ajcord/Eagle-Project/instructions/Deck/1.png

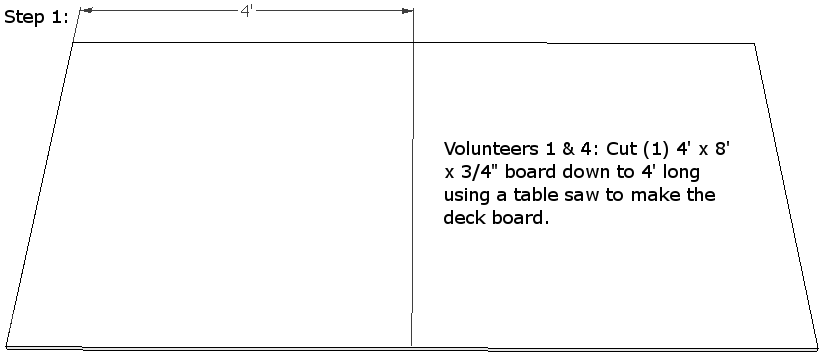
instructions/Deck/1.png
