ajcord/Eagle-Project/instructions/Deck/3.png

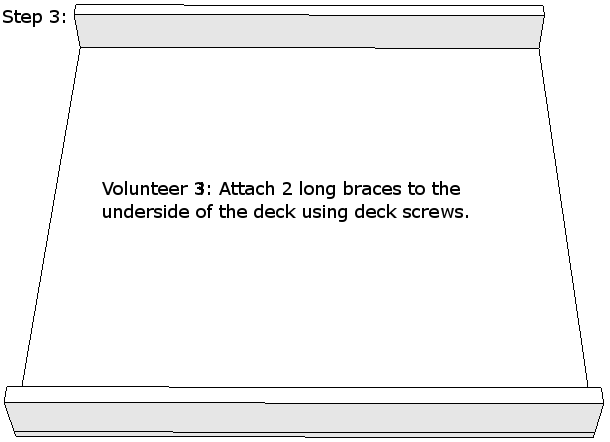
instructions/Deck/3.png
