ajcord/Eagle-Project/instructions/Deck/5.png

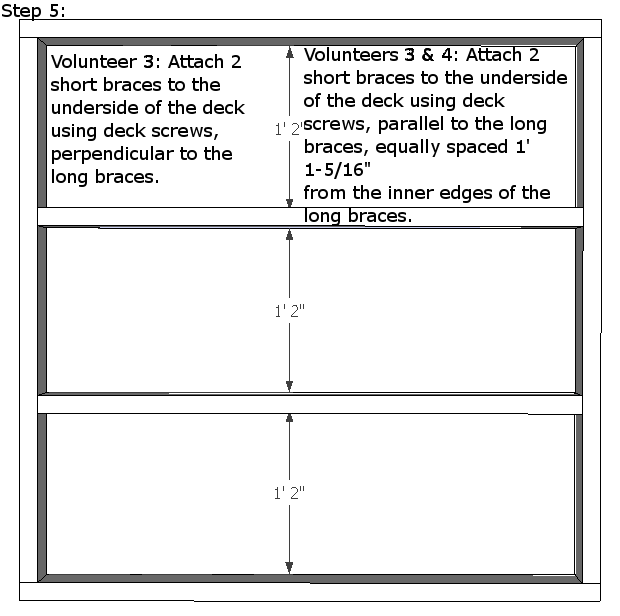
instructions/Deck/5.png
