ajcord/Eagle-Project/instructions/Deck/7.png

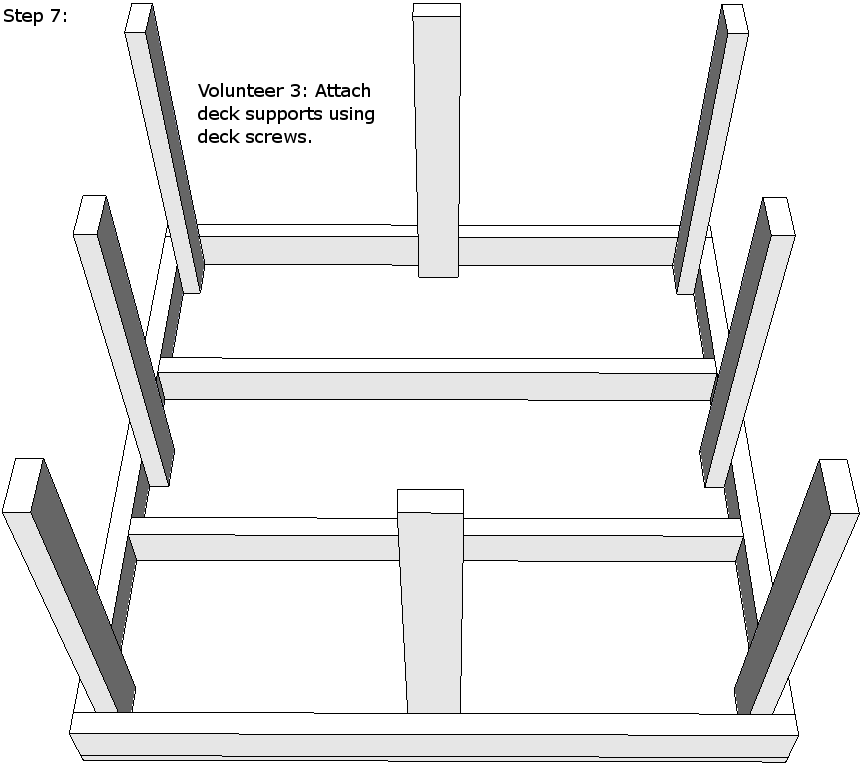
instructions/Deck/7.png
