ajcord/Eagle-Project/instructions/Denver attachment/1.png

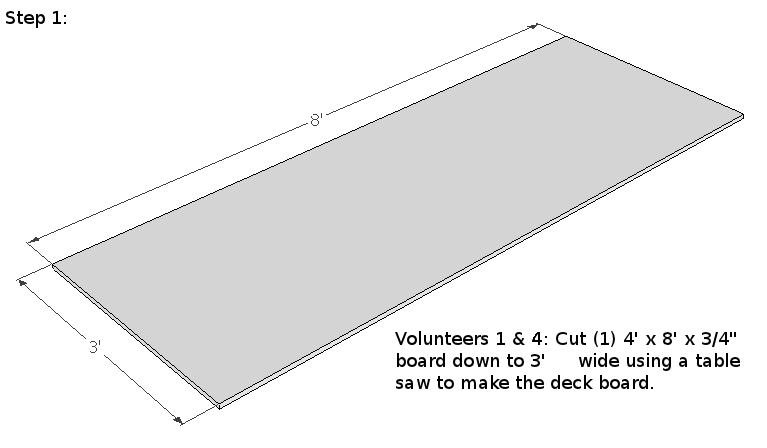
instructions/Denver attachment/1.png
