ajcord/Eagle-Project/instructions/Denver attachment/4.png

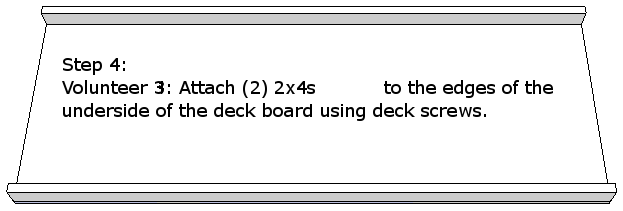
instructions/Denver attachment/4.png
