ajcord/Eagle-Project/instructions/Denver attachment/6.png

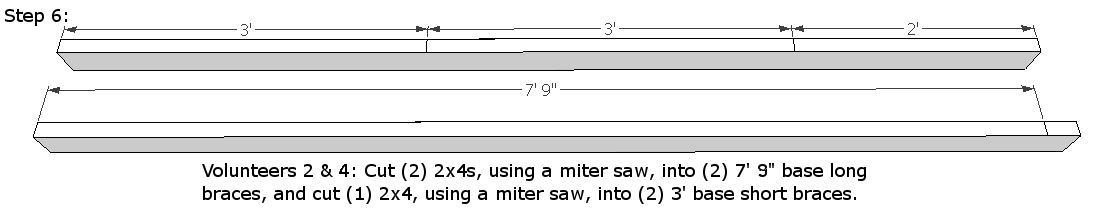
instructions/Denver attachment/6.png
