ajcord/Eagle-Project/instructions/Denver attachment/7.png

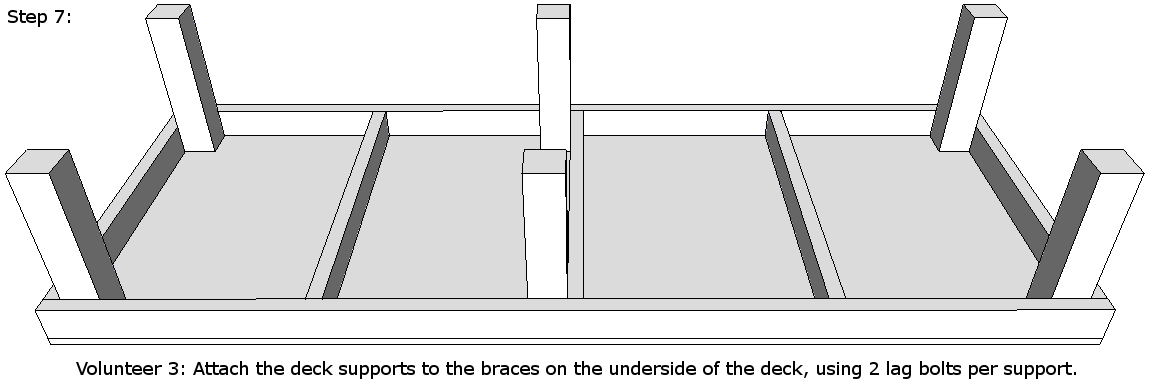
instructions/Denver attachment/7.png
