ajcord/Eagle-Project/instructions/Denver attachment/8.png

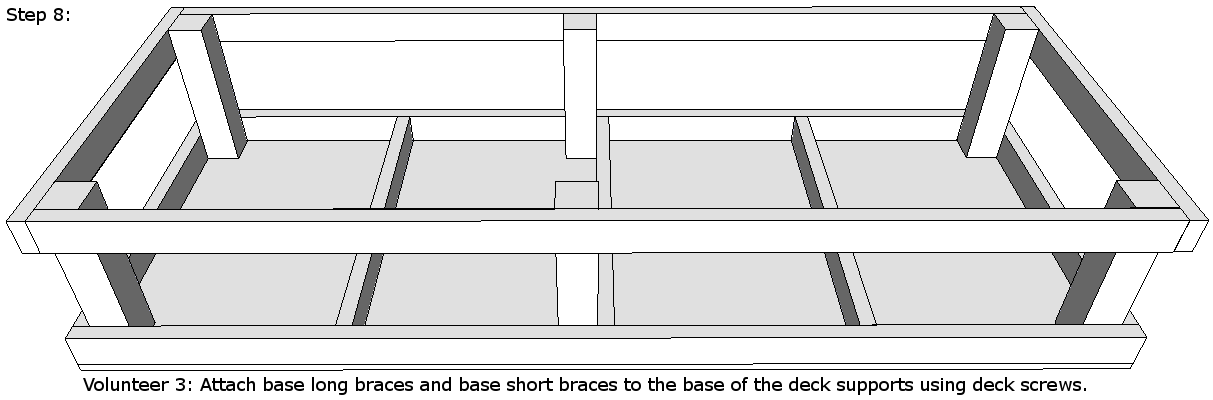
instructions/Denver attachment/8.png
