ajcord/Eagle-Project/instructions/Denver attachment/9.png

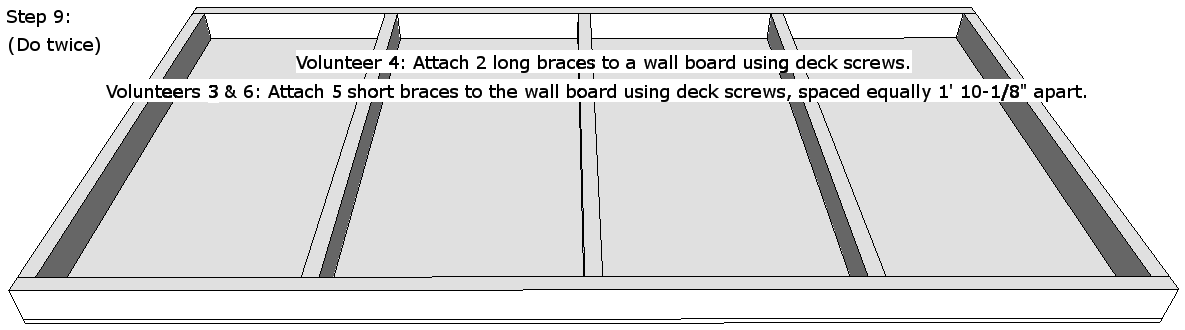
instructions/Denver attachment/9.png
