ajcord/Eagle-Project/instructions/Denver attachment/10.png

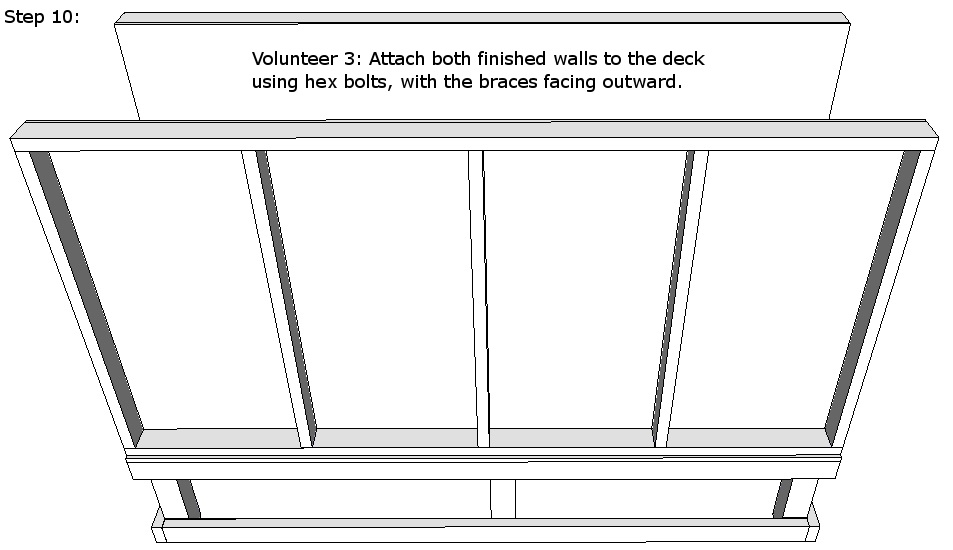
instructions/Denver attachment/10.png
