ajcord/Eagle-Project/instructions/Denver attachment/11.png

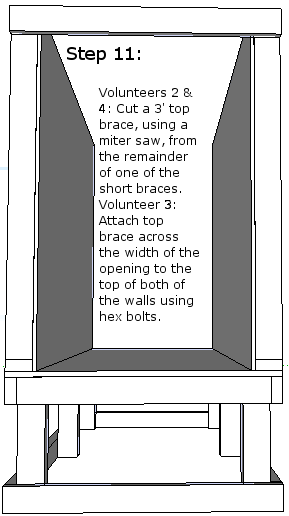
instructions/Denver attachment/11.png
