ajcord/Eagle-Project/instructions/Extras/3.png

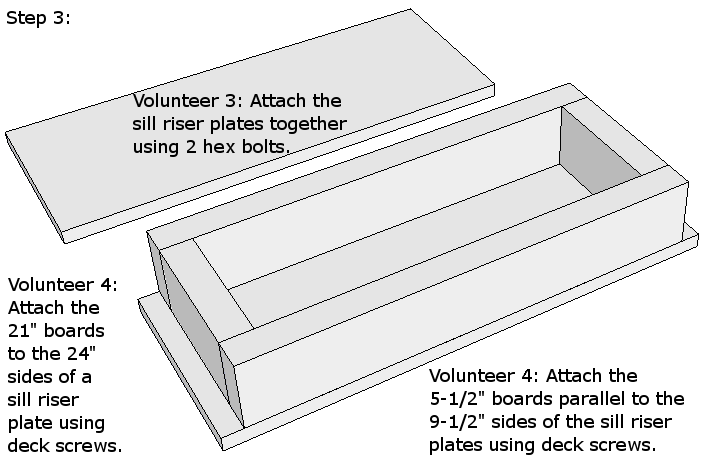
instructions/Extras/3.png
