ajcord/Eagle-Project/instructions/Main wall/1.png

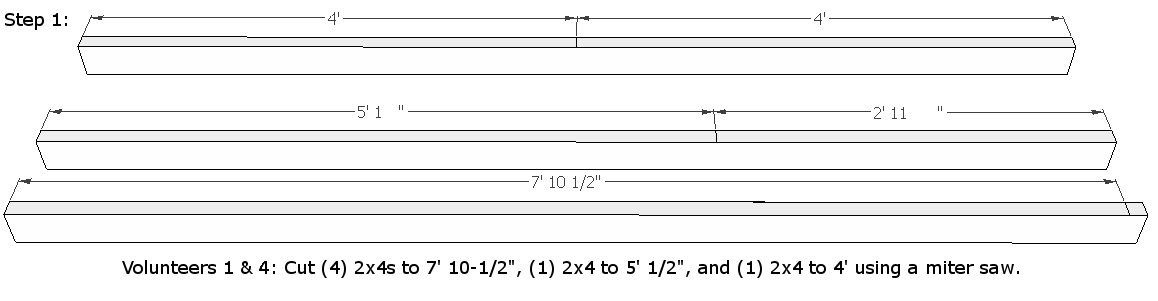
instructions/Main wall/1.png
