ajcord/Eagle-Project/instructions/Main wall/2.png

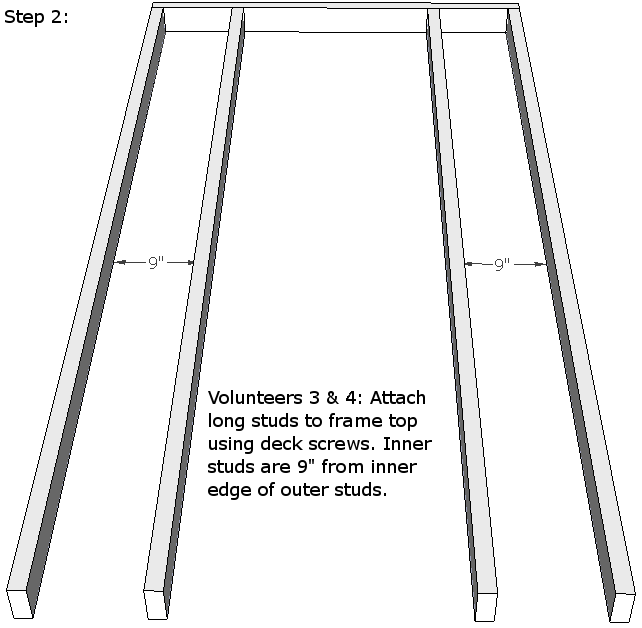
instructions/Main wall/2.png
