ajcord/Eagle-Project/instructions/Main wall/4-2.png

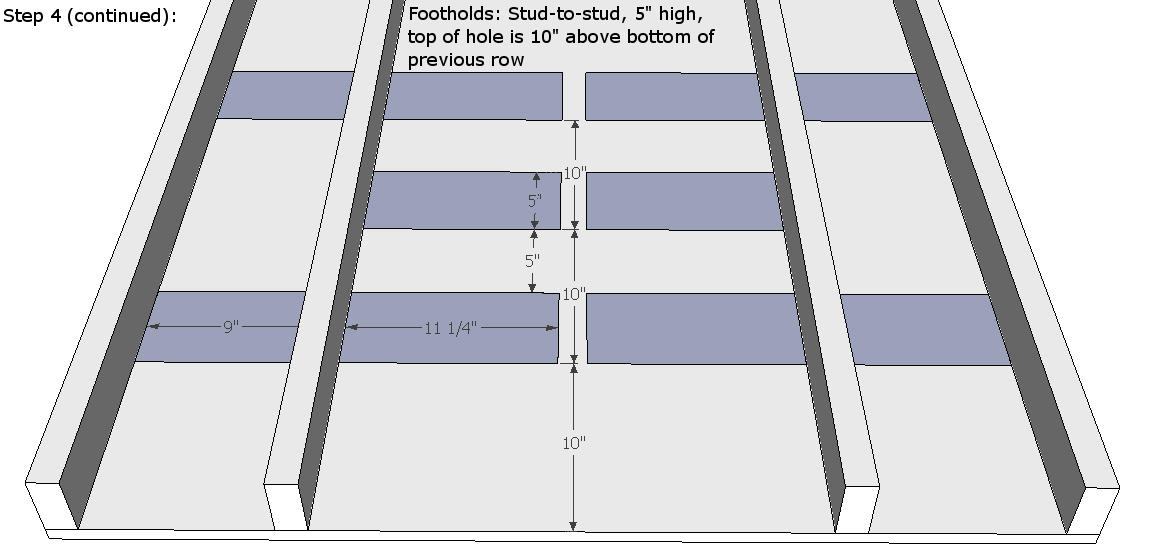
instructions/Main wall/4-2.png
