ajcord/Eagle-Project/instructions/Main wall/4-3.png

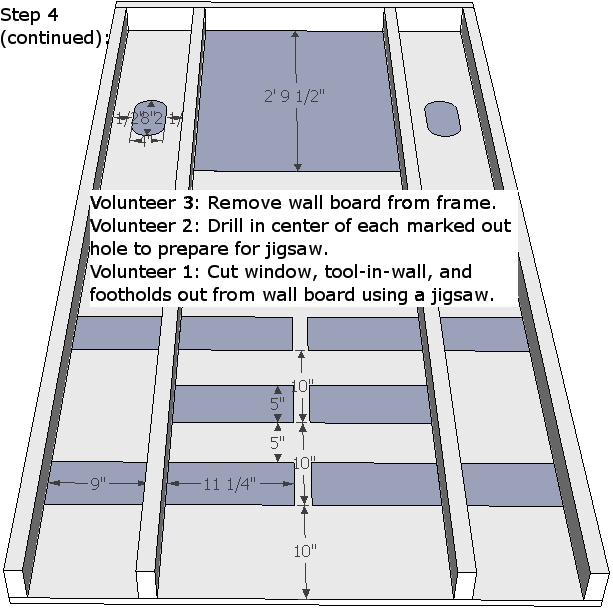
instructions/Main wall/4-3.png
