ajcord/Eagle-Project/instructions/Main wall/4.png

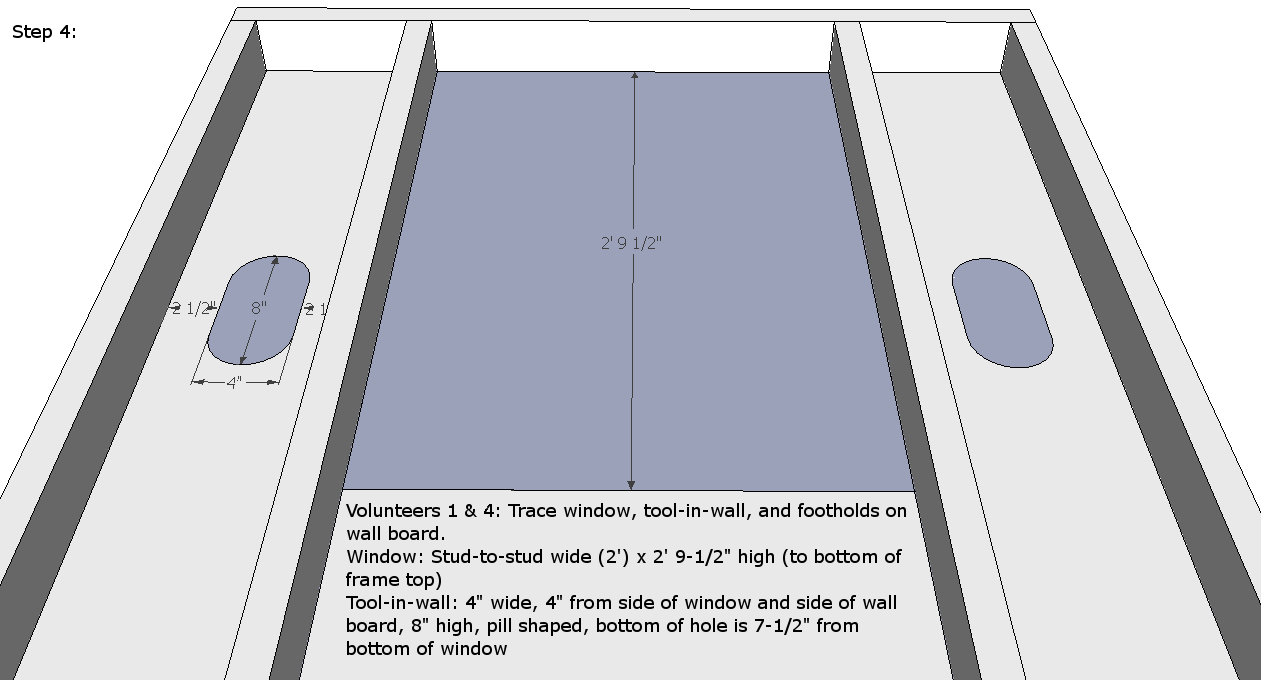
instructions/Main wall/4.png
