ajcord/Eagle-Project/instructions/Main wall/5.png

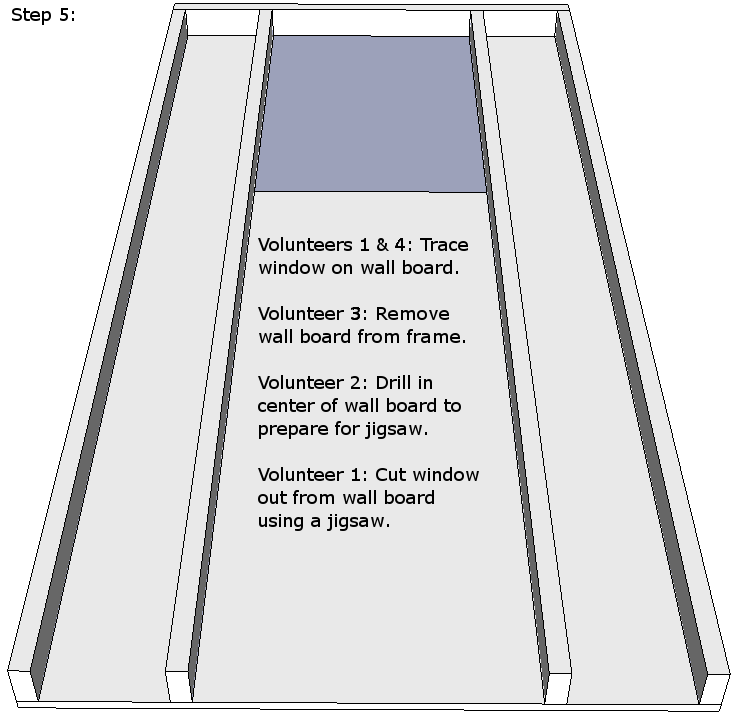
instructions/Main wall/5.png
