ajcord/Eagle-Project/instructions/Main wall/7.png

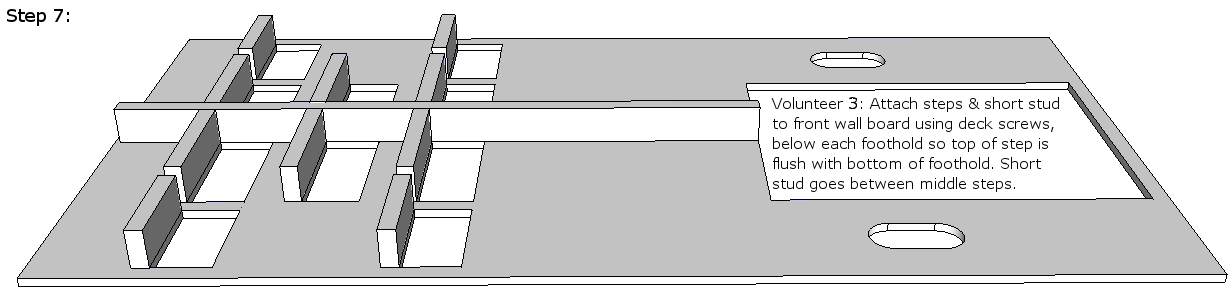
instructions/Main wall/7.png
