ajcord/Eagle-Project/instructions/Main wall/8.png

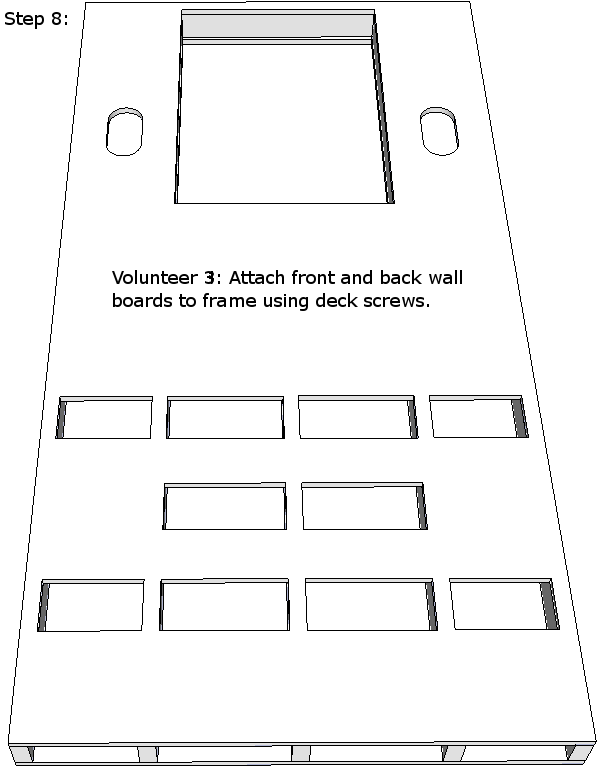
instructions/Main wall/8.png
