ajcord/Eagle-Project/instructions/Main wall/9.png

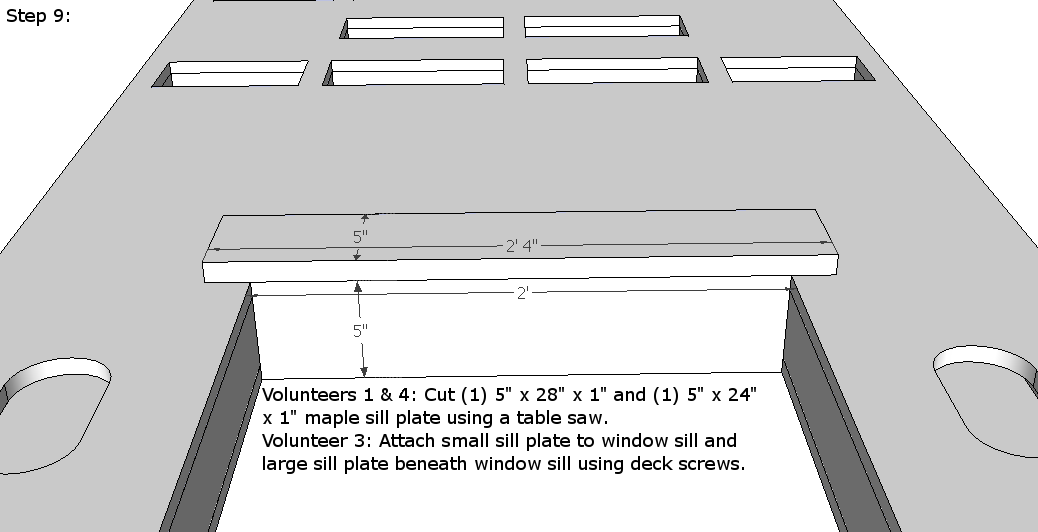
instructions/Main wall/9.png
